Rostikslav/sstk-g9/docs/img/final/EcoSwitch_assembly_left.png

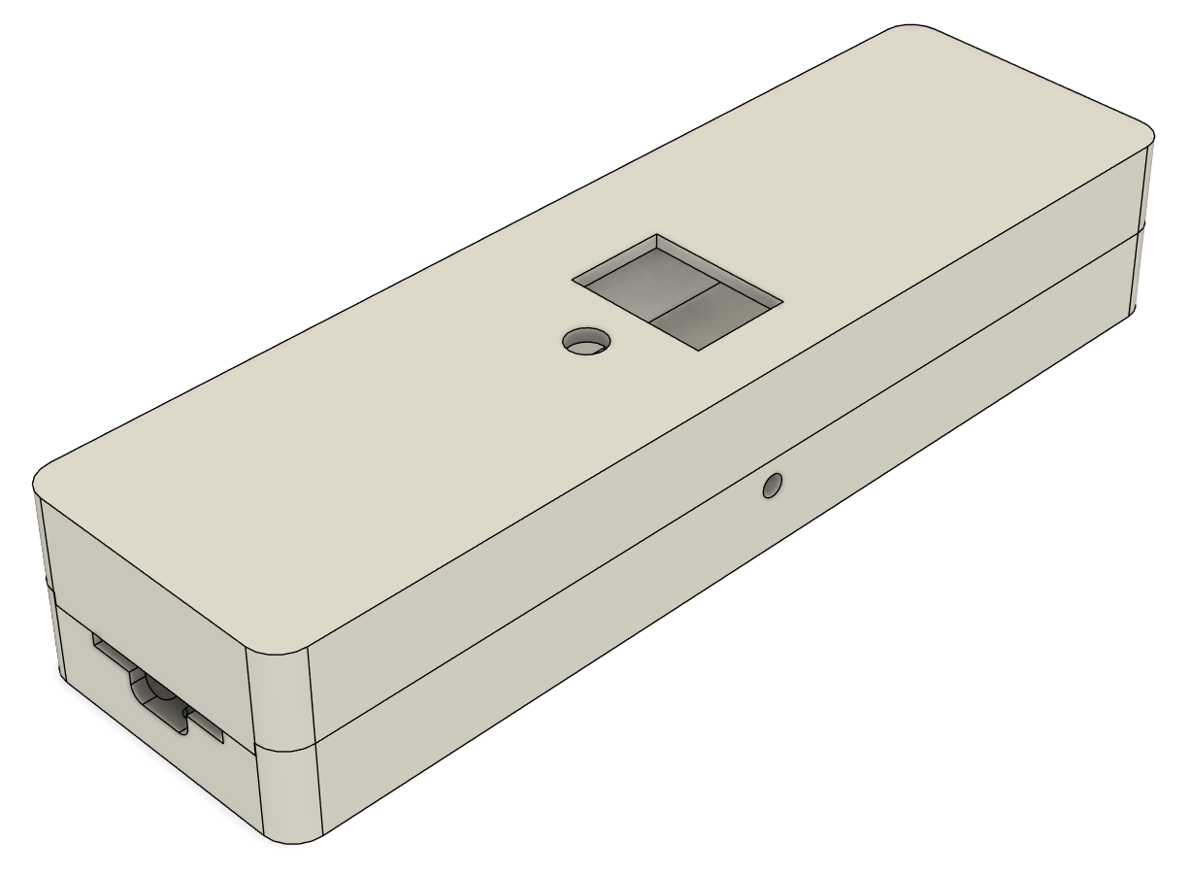
docs/img/final/EcoSwitch_assembly_left.png
