Rostikslav/sstk-g9/docs/img/final/EcoSwitch_assembly_right.png

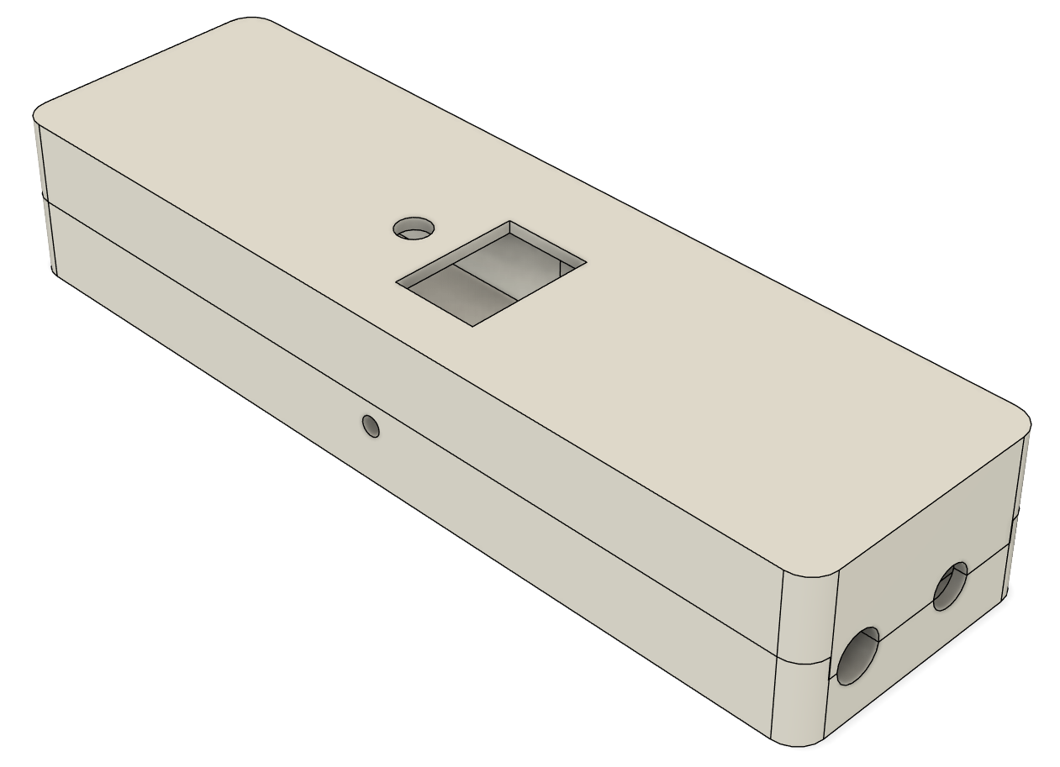
docs/img/final/EcoSwitch_assembly_right.png
